phooky/gronk/firmware/UART.cc

/*
 * Copyright 2010 by Adam Mayer	 <adam@makerbot.com>
 *
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
 * You should have received a copy of the GNU General Public License
 * along with this program.  If not, see <http://www.gnu.org/licenses/>
 */

#include "UART.hh"
#include "CBuf.hh"
#include "Pin.hh"
#include <avr/interrupt.h>
#include <avr/io.h>
#include <avr/sfr_defs.h>
#include <stdint.h>
#include <util/delay.h>

namespace UART {

bool ovfl_in = false;

// We support three platforms: Atmega168 (1 UART), Atmega644, and
// Atmega1280/2560
#if defined(__AVR_ATmega168__) || defined(__AVR_ATmega328__) ||                \
    defined(__AVR_ATmega644P__) || defined(__AVR_ATmega1280__) ||              \
    defined(__AVR_ATmega2560__)
#else
#error UART not implemented on this processor type!
#endif

#if defined(__AVR_ATmega168__) || defined(__AVR_ATmega328__)

#define UBRR_VALUE 25
#define UCSR0A_VALUE 0

#define INIT_SERIAL(uart_)                                                     \
    {                                                                          \
        UBRR0H = UBRR_VALUE >> 8;                                              \
        UBRR0L = UBRR_VALUE & 0xff;                                            \
                                                                               \
        /* set config for uart, explicitly clear TX interrupt flag */          \
        UCSR0A = UCSR0A_VALUE | _BV(TXC0);                                     \
        UCSR0B = _BV(RXEN0) | _BV(TXEN0);                                      \
        UCSR0C = _BV(UCSZ01) | _BV(UCSZ00);                                    \
    }

#elif defined(__AVR_ATmega644P__)

#define UBRR_VALUE 25
#define UBRRA_VALUE 0

// Adapted from ancient arduino/wiring rabbit hole
#define INIT_SERIAL(uart_)                                                     \
    {                                                                          \
        UBRR##uart_##H = UBRR_VALUE >> 8;                                      \
        UBRR##uart_##L = UBRR_VALUE & 0xff;                                    \
                                                                               \
        /* set config for uart_ */                                             \
        UCSR##uart_##A = UBRRA_VALUE;                                          \
        UCSR##uart_##B = _BV(RXEN##uart_) | _BV(TXEN##uart_);                  \
        UCSR##uart_##C = _BV(UCSZ##uart_##1) | _BV(UCSZ##uart_##0);            \
    }

#elif defined(__AVR_ATmega1280__) || defined(__AVR_ATmega2560__)

// Use double-speed mode for more accurate baud rate?
#define UBRR0_VALUE 16 // 115200 baud
#define UBRR1_VALUE 51 // 38400 baud
#define UCSRA_VALUE(uart_) _BV(U2X##uart_)

// Adapted from ancient arduino/wiring rabbit hole
#define INIT_SERIAL(uart_)                                                     \
    {                                                                          \
        UBRR##uart_##H = UBRR##uart_##_VALUE >> 8;                             \
        UBRR##uart_##L = UBRR##uart_##_VALUE & 0xff;                           \
                                                                               \
        /* set config for uart_ */                                             \
        UCSR##uart_##A = UCSRA_VALUE(uart_);                                   \
        UCSR##uart_##B = _BV(RXEN##uart_) | _BV(TXEN##uart_);                  \
        UCSR##uart_##C = _BV(UCSZ##uart_##1) | _BV(UCSZ##uart_##0);            \
    }
#endif

#define ENABLE_SERIAL_INTERRUPTS(uart_)                                        \
    { UCSR##uart_##B |= _BV(RXCIE##uart_) | _BV(TXCIE##uart_); }

#define DISABLE_SERIAL_INTERRUPTS(uart_)                                       \
    { UCSR##uart_##B &= ~(_BV(RXCIE##uart_) | _BV(TXCIE##uart_)); }

CBuf<128, uint8_t> out_buf;
CBuf<128, uint8_t> in_buf;

void initialize() {
    INIT_SERIAL(0);
    enable(true);
}

bool write(uint8_t byte) {
    if (out_buf.empty() && (UCSR0A & (1 << UDRE0))) {
        UDR0 = byte;
        return true;
    } else
        return out_buf.queue(byte);
}

// Queue the given number of bytes of the buffer; returns the
// number of bytes successfully queued
int write_buffer(uint8_t *buf, uint8_t length) {
    int idx = 0;
    while (idx < length) {
        if (!write(buf[idx]))
            return idx;
        idx++;
    }
    return idx;
}

/// Write a null-terminated string to the uart.
int write_string(const char *str, const bool nl) {
    int idx = 0;
    while (str[idx] != 0) {
        if (!write(str[idx]))
            return idx;
        idx++;
    }
    if (nl) {
        write('\r');
        write('\n');
    }
    return idx;
}

/// Return the amount of data available on the uart
int available() { return in_buf.sz; }

/// Read N bytes from the uart into the buffer
/// Returns the number of bytes read
int read(uint8_t *buf, uint8_t n) {
    cli();
    if (in_buf.sz < n) {
        n = in_buf.sz;
    }
    sei();
    uint8_t nc = n;
    while (n) {
        *(buf++) = in_buf.dequeue();
        n--;
    }
    return nc;
}

uint8_t read_byte() { return in_buf.dequeue(); }

void enable(bool enabled) {
    if (enabled) {
        ENABLE_SERIAL_INTERRUPTS(0);
    } else {
        DISABLE_SERIAL_INTERRUPTS(0);
    }
}

} // namespace UART

// Send and receive interrupts
ISR(USART0_RX_vect) {
    UART::ovfl_in = UART::ovfl_in || !UART::in_buf.queue(UDR0);
}

ISR(USART0_TX_vect) {
    if (!UART::out_buf.empty())
        UDR0 = UART::out_buf.dequeue();
}
