phooky/gronk/firmware/parser_test/test.cc

/*
 * Copyright 2010 by Adam Mayer	 <adam@makerbot.com>
 *
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
 * You should have received a copy of the GNU General Public License
 * along with this program.  If not, see <http://www.gnu.org/licenses/>
 */

#include "UART.hh"
#include "CommandParser.hh"
#include <string>
#include <iostream>

using std::string;
namespace UART {

string test_data;
string::const_iterator test_data_iter;

void set_test_string(string data) {
    test_data = data;
    test_data_iter = test_data.begin();
}

// Stubs probably unnecessary
void initialize() {}
bool write(uint8_t byte) { return true; }
int write_buffer(uint8_t *buf, uint8_t length) { return length; }
int write_string(const char *str, const bool nl) { return 0; }
/// Return the amount of data available on the uart
int available() { return test_data.end() - test_data_iter; }

/// Returns the number of bytes read
int read(uint8_t *buf, uint8_t n) {
    if (available() < n) {
        n = available();
    }
    int nc = n;
    while (n) {
        *(buf++) = *(test_data_iter++);
        n--;
    }
    return nc;
}

uint8_t read_byte() { return *(test_data_iter++); }

void enable(bool enabled) {}

} // namespace UART


const char codes[] = { 'X', 'Y', 'Z', 'P', 'S', 'F' };

void run_test(const string s) {
    cmd().reset();
    UART::set_test_string(s);
    std::cout << s;
    if (!check_for_command()) {
        std::cout << "unfinished" << std::endl;
    } else if (!cmd().is_ok()) {
        std::cout << "error" << std::endl;
    } else {
        std::cout << "command " << cmd().code().code << (int)cmd().code().value << std::endl;
        for (const char& code : codes) {
            uint8_t idx = paramIdx(code);
            if (cmd().has_param(idx)) {
                std::cout << "parameter " << code << " = " << cmd()[idx] << std::endl;
            }
        }

    }
    std::cout << " --- --- --- " << std::endl;
}

int main() {
    run_test("G00X10 P5 Y10 F20\n\r");
    run_test("G02X10 P5 Y10 F20\n\r");
    run_test("G02X10 P5 Y10 F20 ; end comment\n\r");
    run_test("; just comment \n\r");
    run_test("G02 X10P5Y10F20\n\r");
}
